YUKESH0620/ESP32-C3-Sensor-PCB/hardware_v0.2_Improved/Kicad_files_v0.2/images_v0.2/PCB_v0.2/Screenshot 2025-12-28 115842.png

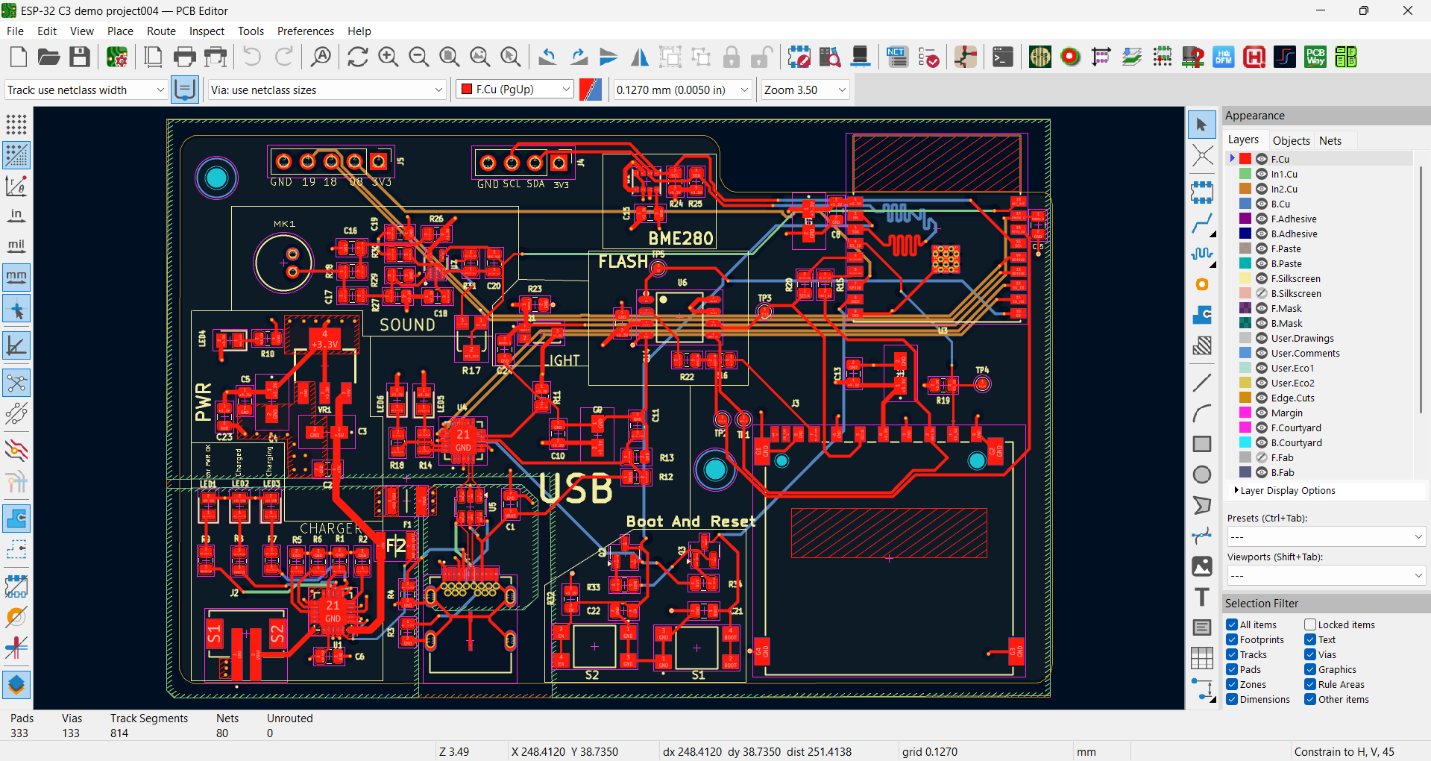
hardware_v0.2_Improved/Kicad_files_v0.2/images_v0.2/PCB_v0.2/Screenshot 2025-12-28 115842.png
