YUKESH0620/ESP32-C3-Sensor-PCB/hardware_v0.2_Improved/Kicad_files_v0.2/images_v0.2/Schematic_View_v0.2/Screenshot 2025-12-30 061500.png

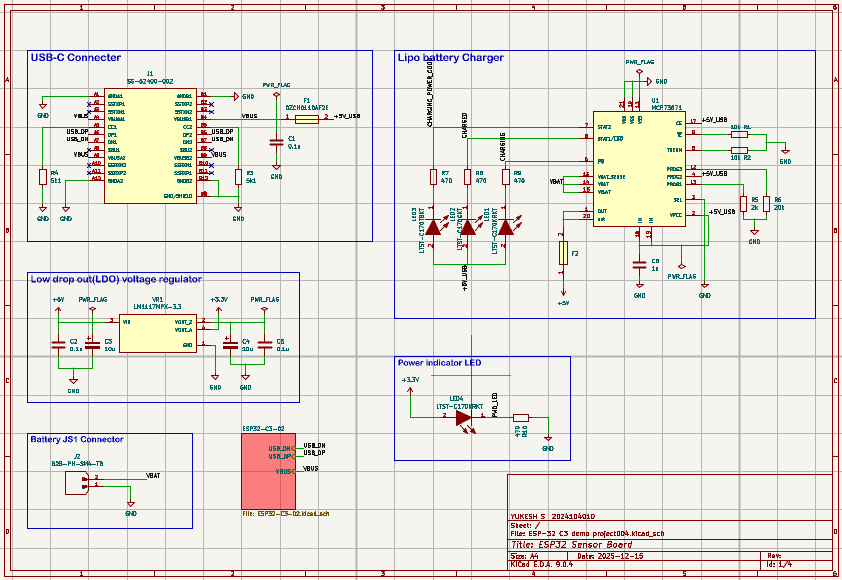
hardware_v0.2_Improved/Kicad_files_v0.2/images_v0.2/Schematic_View_v0.2/Screenshot 2025-12-30 061500.png
