YUKESH0620/ESP32-C3-Sensor-PCB/images/PCB_Layout/Screenshot 2025-12-26 091120.png

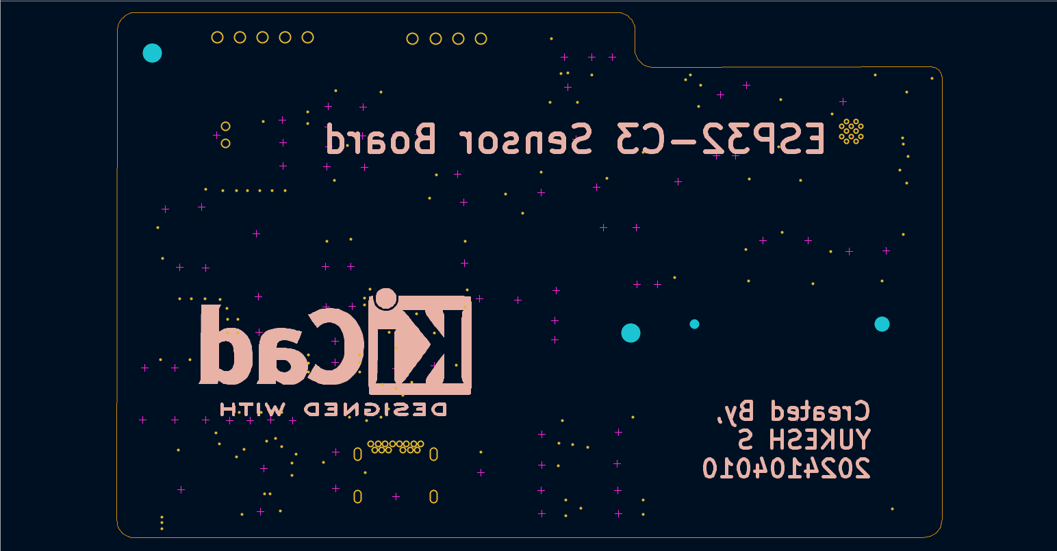
images/PCB_Layout/Screenshot 2025-12-26 091120.png
