YUKESH0620/ESP32-C3-Sensor-PCB/docs/External_Design_Blocks/USLPT2819DT2TR.step

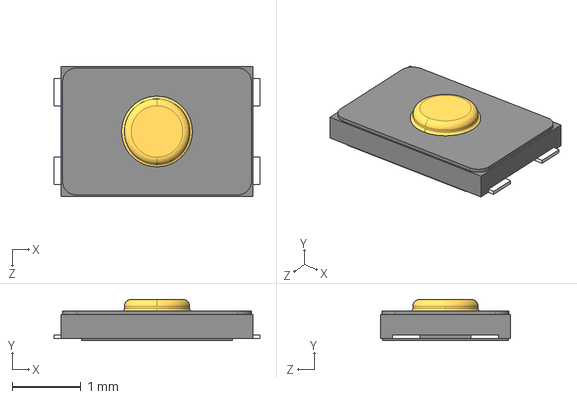
[picture p31: CAD file, 2025-12-26]
docs/External_Design_Blocks/USLPT2819DT2TR.step
3.00 x 0.6 x 1.90 mm
