YUKESH0620/ESP32-C3-Sensor-PCB/docs/External_Design_Blocks/TP4056.step

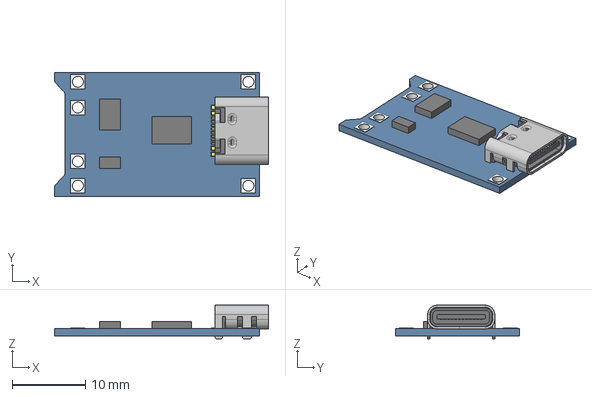
[picture p32: CAD file, 2025-12-26]
docs/External_Design_Blocks/TP4056.step
29.3 x 17.0 x 4.60 mm
