YUKESH0620/ESP32-C3-Sensor-PCB/docs/External_Design_Blocks/USB4110GFA.step

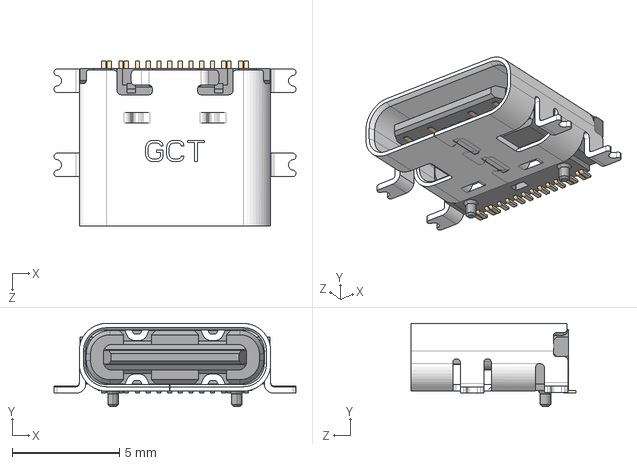
[picture p33: CAD file, 2025-12-26]
docs/External_Design_Blocks/USB4110GFA.step
11.3 x 3.89 x 7.70 mm
