YUKESH0620/ESP32-C3-Sensor-PCB/docs/External_Design_Blocks/1-2295018-2.step

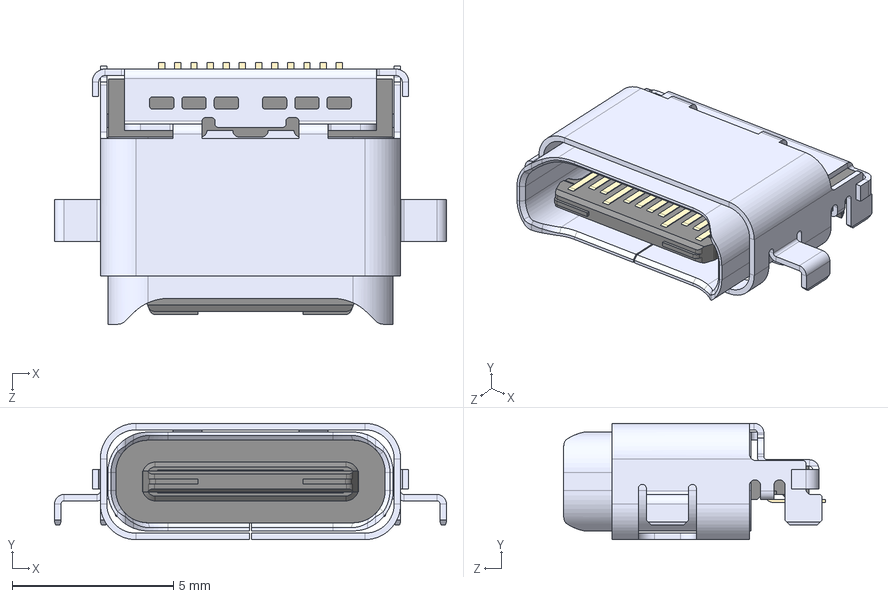
[picture p34: CAD file, 2025-12-26]
docs/External_Design_Blocks/1-2295018-2.step
12.1 x 3.60 x 8.10 mm
