YUKESH0620/ESP32-C3-Sensor-PCB/hardware/Schematic_view/ESP32-C3-02.kicad_sch

## KiCad design hardware/Schematic_view/ESP32-C3-02.kicad_sch (2025-12-26)

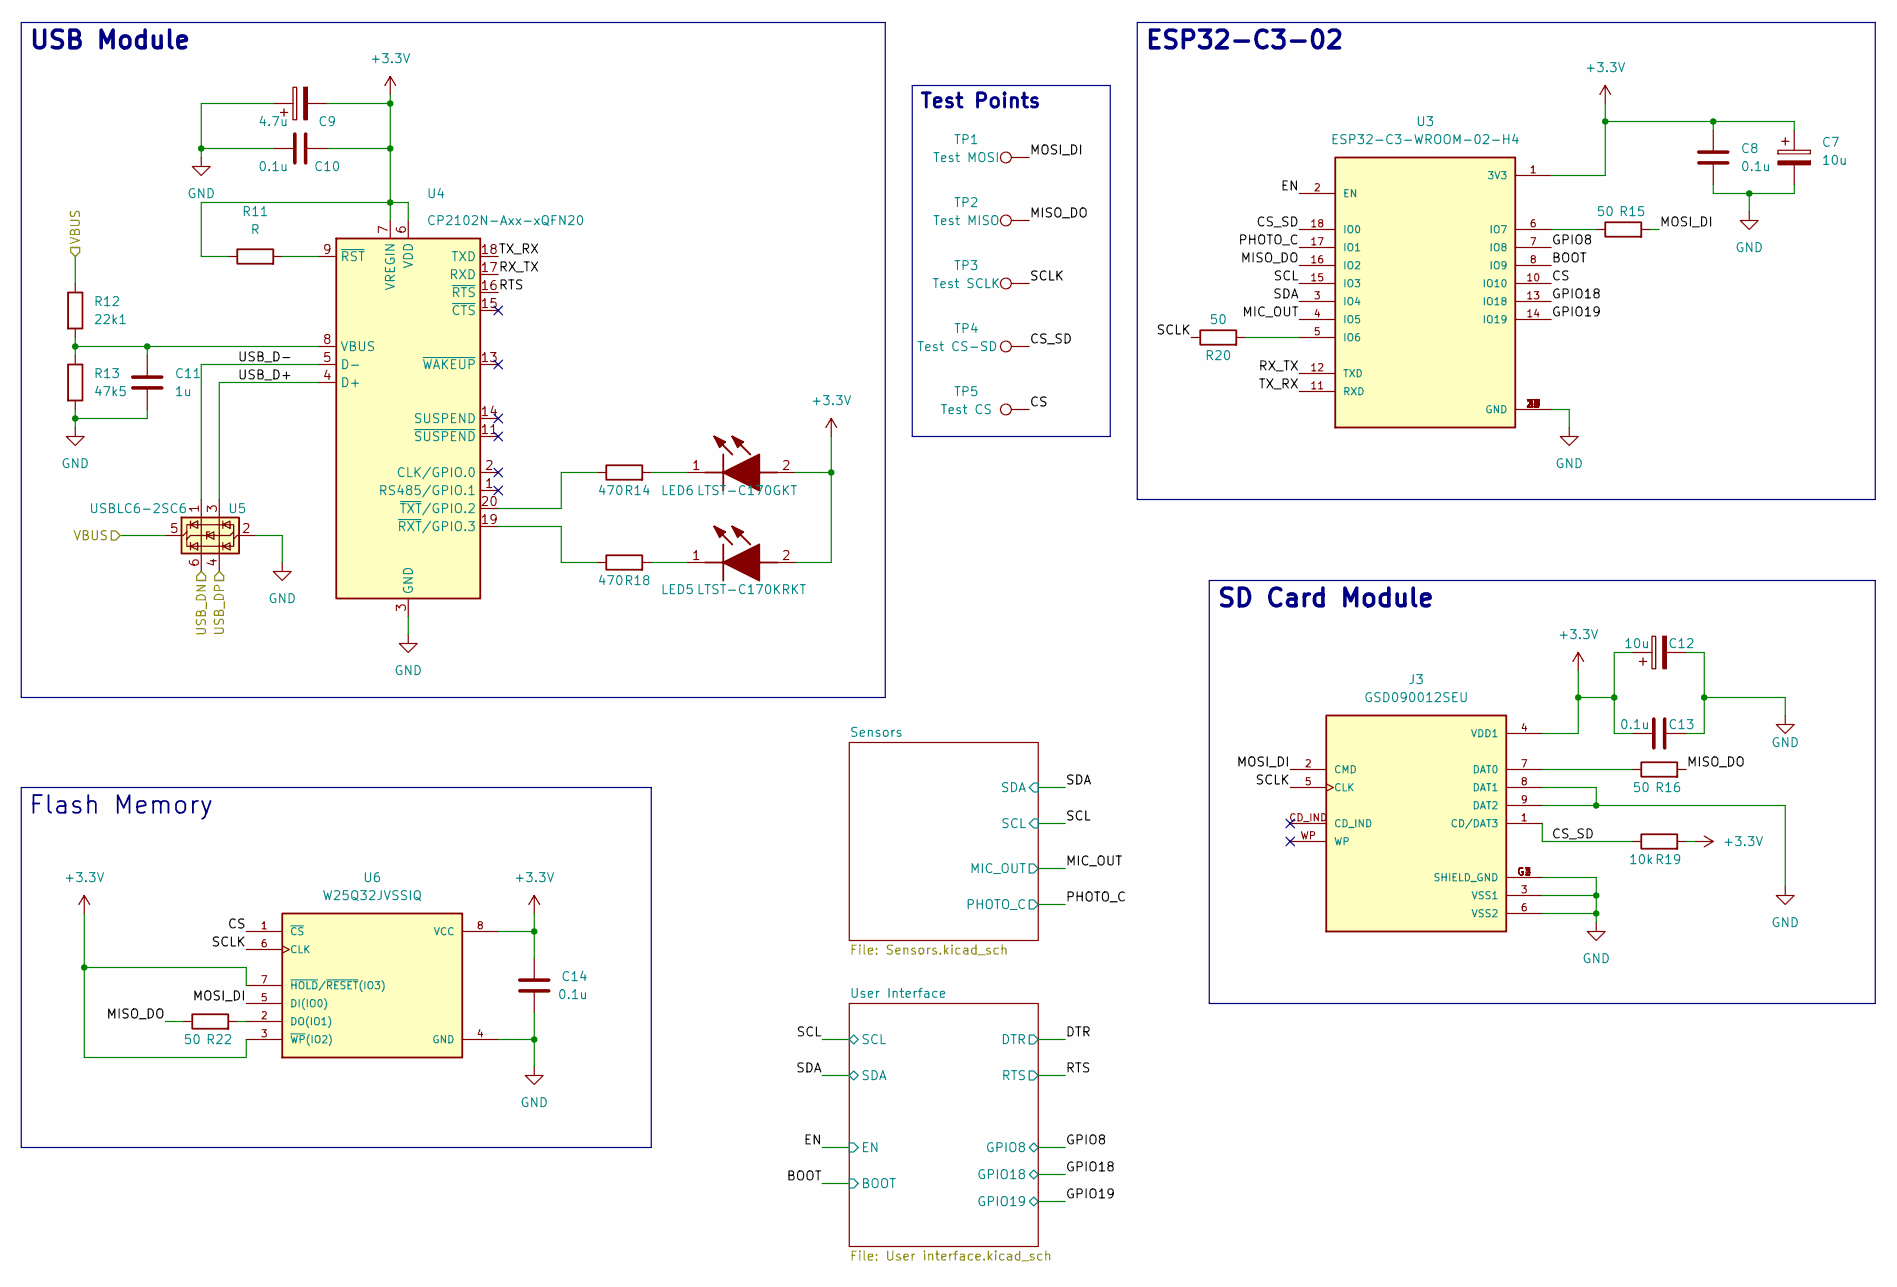
[picture p36: schematic ESP32-C3-02.kicad_sch]

Parts:
C7, C12: 10u; T491A
C8, C10, C13, C14: 0.1u; C_0805_2012Metric
C9: 4.7u; T491A
C11: 1u; C_0805_2012Metric
J3: GSD090012SEU; AMPHENOL_GSD090012SEU; PARTREV E
LED5: LTST-C170GKT; LEDC2012X120N; Manufacturer_Part_Number LTST-C170GKT; Mouser Part Number 859-LTST-C170GKT
LED6: LTST-C170KRKT; LEDC2012X120N; Manufacturer_Part_Number LTST-C170KRKT; Mouser Part Number 859-LTST-C170KRKT
R11: R; R_0805_2012Metric
R12: 22k1; R_0805_2012Metric
R13: 47k5; R_0805_2012Metric
R14, R18: 470; R_0805_2012Metric
R15, R16, R20, R22: 50; R_0805_2012Metric
R19: 10k; R_0805_2012Metric
TP1: Test MOSI; TestPoint_Pad_D1.0mm
TP2: Test MISO; TestPoint_Pad_D1.0mm
TP3: Test SCLK; TestPoint_Pad_D1.0mm
TP4: Test CS-SD; TestPoint_Pad_D1.0mm
TP5: Test CS; TestPoint_Pad_D1.0mm
U3: ESP32-C3-WROOM-02-H4; MODULE_ESP32-C3-WROOM-02-H4
U4: CP2102N-Axx-xQFN20; QFN50P400X400X100-21N
U5: USBLC6-2SC6; SOT-23-6
U6: W25Q32JVSSIQ; SOIC127P790X216-8N; M_PART_NUMBER W25QXX

Connections:
+3.3V: C7.1, C8.1, C9.2, C10.2, C12.1, C13.1, C14.2, J3.4 (VDD1), LED5.2 (A), LED6.2 (A), R11.1, R19.2, U3.1 (3V3), U4.6 (VDD), U4.7 (VREGIN), U6.3 (~WP(IO2)), U6.7 (~HOLD/~RESET(IO3)), U6.8 (VCC)
BOOT: U3.8 (IO9)
CS: TP5.1, U3.10 (IO10), U6.1 (~CS)
CS_SD: J3.1 (CD/DAT3), R19.1, TP4.1, U3.18 (IO0)
EN: U3.2 (EN)
GND: C7.2, C8.2, C9.1, C10.1, C11.2, C12.2, C13.2, C14.1, J3.3 (VSS1), J3.6 (VSS2), J3.8 (DAT1), J3.9 (DAT2), J3.G1 (SHIELD_GND), J3.G2 (SHIELD_GND), J3.G3 (SHIELD_GND), J3.G4 (SHIELD_GND), R13.2, U3.9 (GND), U3.19 (GND), U3.20 (GND), U3.21 (GND), U3.22 (GND), U3.23 (GND), U3.24 (GND), U3.25 (GND), U3.26 (GND), U3.27 (GND), U3.28 (GND), U3.29 (GND), U3.30 (GND), U3.31 (GND), U3.32 (GND), U3.33 (GND), U3.34 (GND), U3.35 (GND), U3.36 (GND), U3.37 (GND), U3.38 (GND), U3.39 (GND), U4.3 (GND), U4.12 (GND), U4.21 (GND), U5.2 (GND), U6.4 (GND)
GPIO8: U3.7 (IO8)
GPIO18: U3.13 (IO18)
GPIO19: U3.14 (IO19)
MIC_OUT: U3.4 (IO5)
MISO_DO: R16.2, R22.1, TP2.1, U3.16 (IO2)
MOSI_DI: J3.2 (CMD), R15.2, TP1.1, U6.5 (DI(IO0))
unnamed: C11.1, R12.2, R13.1, U4.8 (VBUS)
unnamed: J3.7 (DAT0), R16.1
unnamed: LED5.1 (K), R14.2
unnamed: LED6.1 (K), R18.2
unnamed: R11.2, U4.9 (~RST)
unnamed: R14.1, U4.20 (~TXT/GPIO.2)
unnamed: R15.1, U3.6 (IO7)
unnamed: R18.1, U4.19 (~RXT/GPIO.3)
unnamed: R20.2, U3.5 (IO6)
unnamed: R22.2, U6.2 (DO(IO1))
PHOTO_C: U3.17 (IO1)
RTS: U4.16 (~RTS)
RX_TX: U3.12 (TXD), U4.17 (RXD)
SCL: U3.15 (IO3)
SCLK: J3.5 (CLK), R20.1, TP3.1, U6.6 (CLK)
SDA: U3.3 (IO4)
TX_RX: U3.11 (RXD), U4.18 (TXD)
USB_D+: U4.4 (D+), U5.3 (I/O2)
USB_D-: U4.5 (D-), U5.1 (I/O1)
USB_DN: U5.6 (I/O1)
USB_DP: U5.4 (I/O2)
VBUS: R12.1, U5.5 (VBUS)

Notes on the sheet:
SD Card Module
Flash Memory
ESP32-C3-02
Test Points
USB Module
