YUKESH0620/ESP32-C3-Sensor-PCB/hardware/Schematic_view/ESP-32 C3 demo project004.kicad_sch

## KiCad design hardware/Schematic_view/ESP-32 C3 demo project004.kicad_sch (2025-12-26)

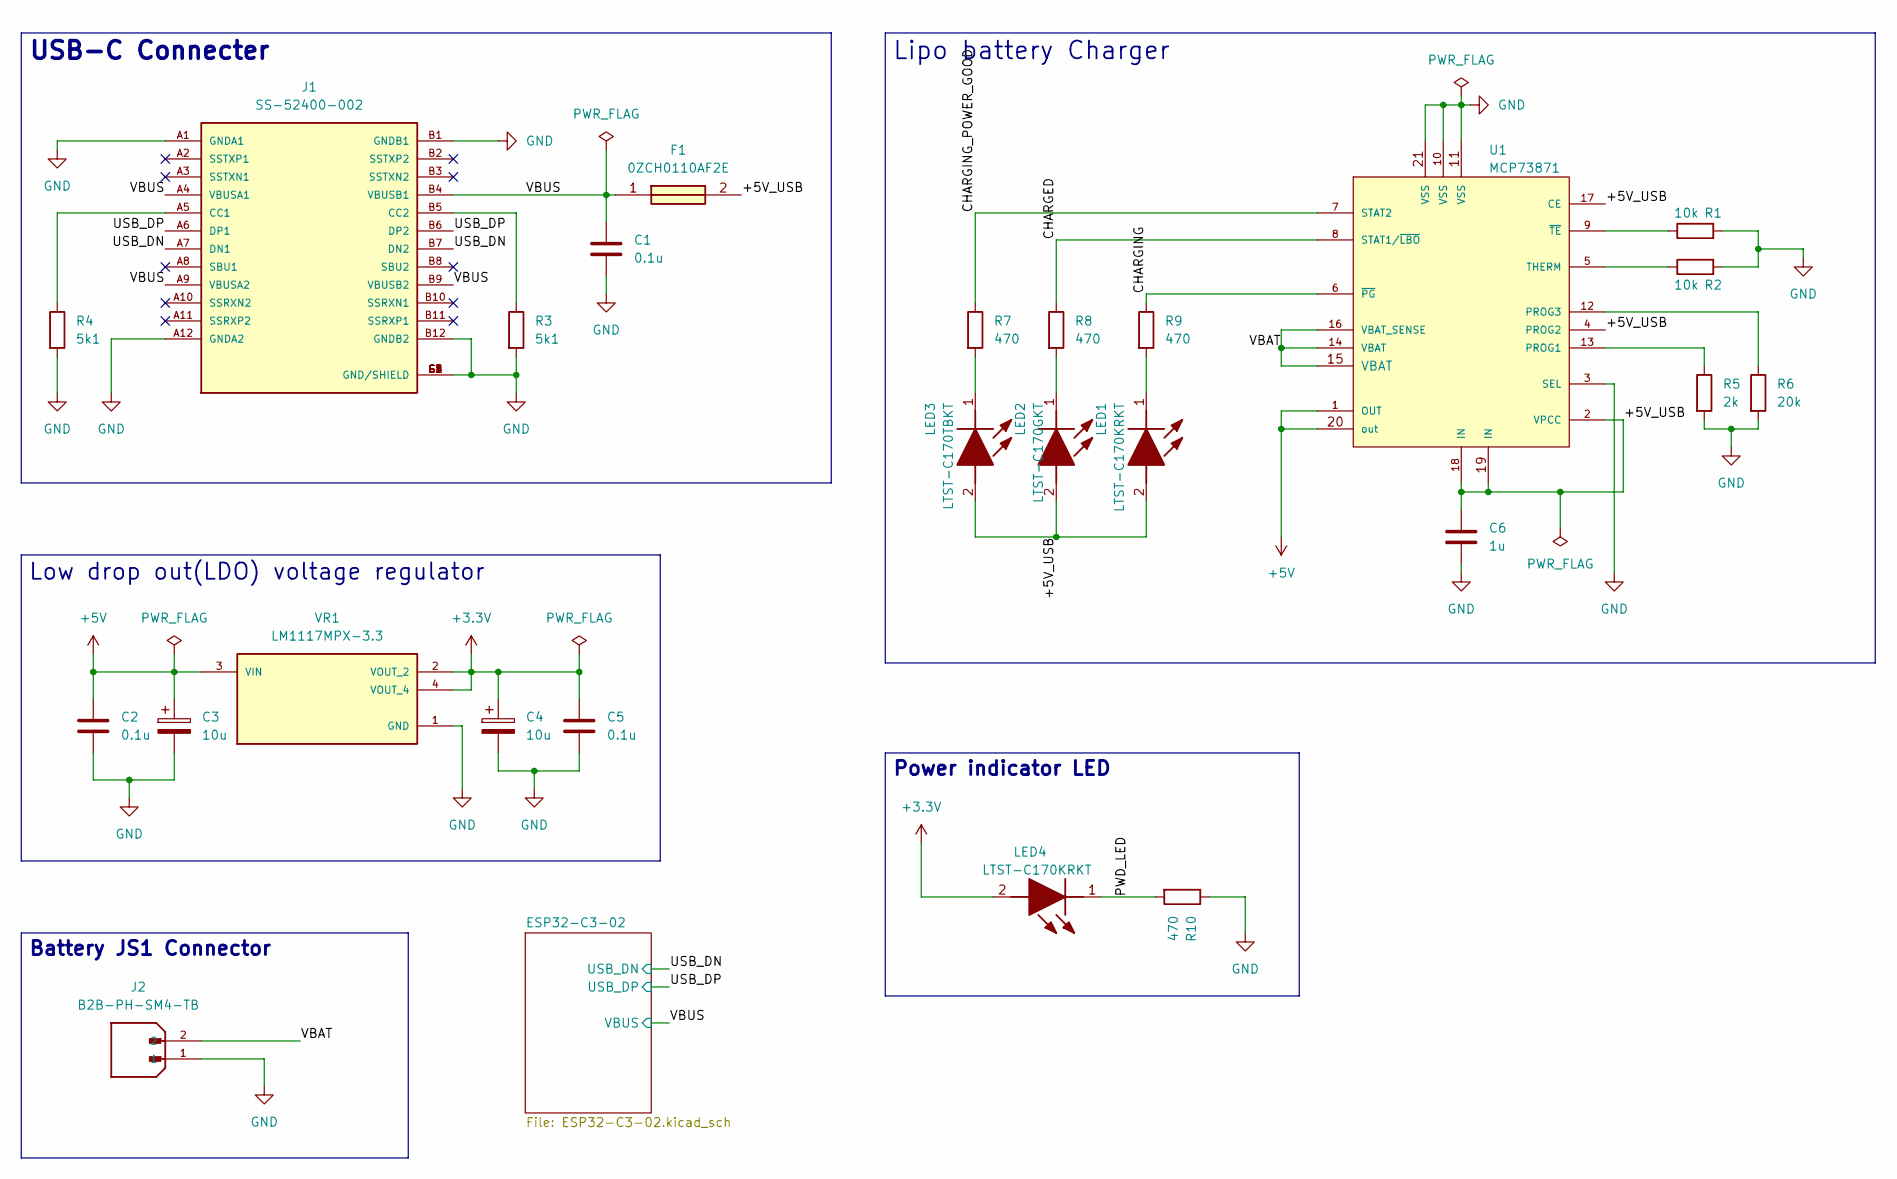
[picture p37: schematic ESP-32 C3 demo project004.kicad_sch]

Parts:
C1, C2, C5: 0.1u; C_0805_2012Metric
C3, C4: 10u; T491A
C6: 1u; C_0805_2012Metric
F1: 0ZCH0110AF2E; FUSC3226X100N; Manufacturer_Part_Number 0ZCH0110AF2E
J1: SS-52400-002; BELFUSE_SS-52400-002; PARTREV A0
J2: B2B-PH-SM4-TB; JST_B2B-PH-SM4-TB; PARTREV N/A
LED1, LED4: LTST-C170KRKT; LEDC2012X120N; Manufacturer_Part_Number LTST-C170KRKT; Mouser Part Number 859-LTST-C170KRKT
LED2: LTST-C170GKT; LEDC2012X120N; Manufacturer_Part_Number LTST-C170GKT; Mouser Part Number 859-LTST-C170GKT
LED3: LTST-C170TBKT; LEDC2012X120N; Manufacturer_Part_Number LTST-C170TBKT; Mouser Part Number 859-LTST-C170TBKT
R1, R2: 10k; R_0805_2012Metric
R3, R4: 5k1; R_0805_2012Metric
R5: 2k; R_0805_2012Metric
R6: 20k; R_0805_2012Metric
R7, R8, R9, R10: 470; R_0805_2012Metric
U1: MCP73871; QFN50P400X400X100-21N; PARTREV D
VR1: LM1117MPX-3.3; VREG_LM1117MPX-3.3

Connections:
+3.3V: C4.1, C5.1, LED4.2 (A), VR1.2 (VOUT_2), VR1.4 (VOUT_4)
+5V: C2.1, C3.1, U1.1 (OUT), U1.20 (out), VR1.3 (VIN)
+5V_USB: C6.1, F1.2, LED1.2 (A), LED2.2 (A), LED3.2 (A), U1.2 (VPCC), U1.4 (PROG2), U1.17 (CE), U1.18 (IN), U1.19 (IN)
CHARGED: R8.1, U1.8 (STAT1/~LBO)
CHARGING: R9.1, U1.6 (~PG)
CHARGING_POWER_GOOD: R7.1, U1.7 (STAT2)
GND: C1.2, C2.2, C3.2, C4.2, C5.2, C6.2, J1.A1 (GNDA1), J1.A12 (GNDA2), J1.B1 (GNDB1), J1.B12 (GNDB2), J1.G1 (GND/SHIELD), J1.G2 (GND/SHIELD), J1.G3 (GND/SHIELD), J1.G4 (GND/SHIELD), J1.S1 (GND/SHIELD), J1.S2 (GND/SHIELD), J1.S3 (GND/SHIELD), J1.S4 (GND/SHIELD), J2.1, R1.2, R2.2, R3.2, R4.2, R5.2, R6.2, R10.1, U1.3 (SEL), U1.10 (VSS), U1.11 (VSS), U1.21 (VSS), VR1.1 (GND)
unnamed: J1.A5 (CC1), R4.1
unnamed: J1.B5 (CC2), R3.1
unnamed: LED1.1 (K), R9.2
unnamed: LED2.1 (K), R8.2
unnamed: LED3.1 (K), R7.2
unnamed: R1.1, U1.9 (~TE)
unnamed: R2.1, U1.5 (THERM)
unnamed: R5.1, U1.13 (PROG1)
unnamed: R6.1, U1.12 (PROG3)
PWD_LED: LED4.1 (K), R10.2
USB_DN: J1.A7 (DN1), J1.B7 (DN2)
USB_DP: J1.A6 (DP1), J1.B6 (DP2)
VBAT: J2.2, U1.14 (VBAT), U1.15 (VBAT), U1.16 (VBAT_SENSE)
VBUS: C1.1, F1.1, J1.A4 (VBUSA1), J1.A9 (VBUSA2), J1.B4 (VBUSB1), J1.B9 (VBUSB2)

Notes on the sheet:
Lipo battery Charger
USB-C Connecter
Power indicator LED
Battery JS1 Connector
Low drop out(LDO) voltage regulator
