YUKESH0620/ESP32-C3-Sensor-PCB/hardware/Schematic_view/Sensors.kicad_sch

## KiCad design hardware/Schematic_view/Sensors.kicad_sch (2025-12-26)

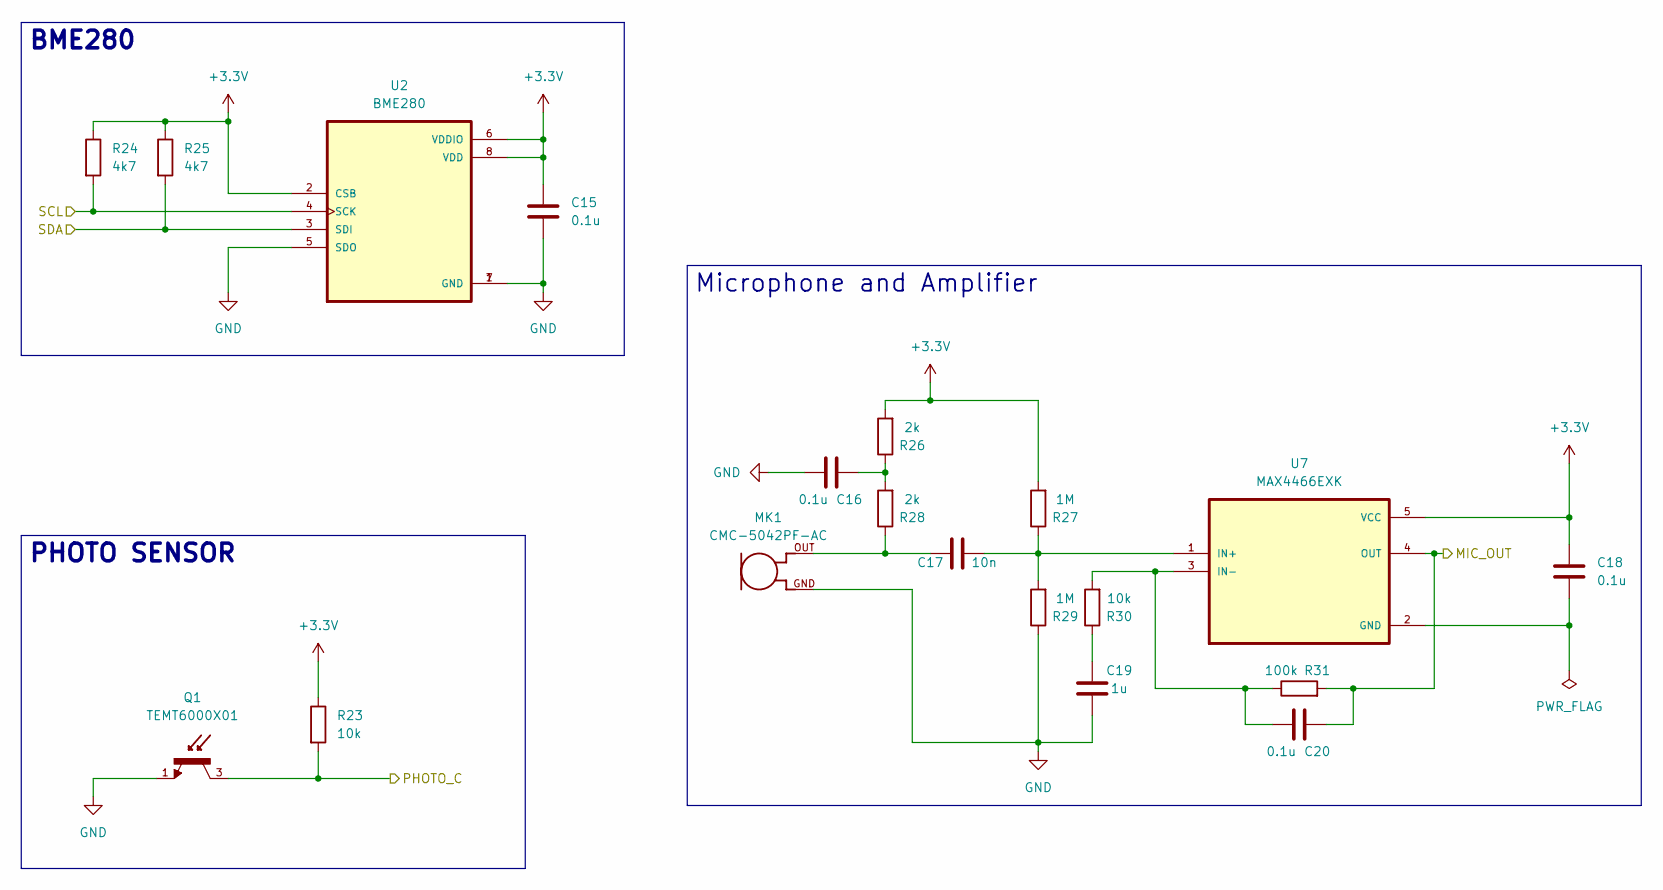
[picture p38: schematic Sensors.kicad_sch]

Parts:
C15, C16, C18, C20: 0.1u; C_0805_2012Metric
C17: 10n; C_0805_2012Metric
C19: 1u; C_0805_2012Metric
MK1: CMC-5042PF-AC; CUI_CMC-5042PF-AC
Q1: TEMT6000X01; TRANS_TEMT6000X01; PARTREV 1.9
R23, R30: 10k; R_0805_2012Metric
R24, R25: 4k7; R_0805_2012Metric
R26, R28: 2k; R_0805_2012Metric
R27, R29: 1M; R_0805_2012Metric
R31: 100k; R_0805_2012Metric
U2: BME280; PSON65P250X250X100-8N
U7: MAX4466EXK; SOT65P210X110-5N

Connections:
+3.3V: C15.1, C18.1, R23.1, R24.1, R25.1, R26.2, R27.2, U2.2 (CSB), U2.6 (VDDIO), U2.8 (VDD), U7.5 (VCC)
GND: C15.2, C16.1, C19.1, MK1.GND, Q1.1, R29.1, U2.1 (GND), U2.5 (SDO), U2.7 (GND)
MIC_OUT: C20.2, R31.2, U7.4 (OUT)
unnamed: C16.2, R26.1, R28.2
unnamed: C17.1, R27.1, R29.2, U7.1 (IN+)
unnamed: C17.2, MK1.OUT, R28.1
unnamed: C18.2, U7.2 (GND)
unnamed: C19.2, R30.1
unnamed: C20.1, R30.2, R31.1, U7.3 (IN-)
PHOTO_C: Q1.3, R23.2
SCL: R24.2, U2.4 (SCK)
SDA: R25.2, U2.3 (SDI)

Notes on the sheet:
BME280
Microphone and Amplifier
PHOTO SENSOR
