YUKESH0620/ESP32-C3-Sensor-PCB/hardware/Schematic_view/User interface.kicad_sch

## KiCad design hardware/Schematic_view/User interface.kicad_sch (2025-12-26)

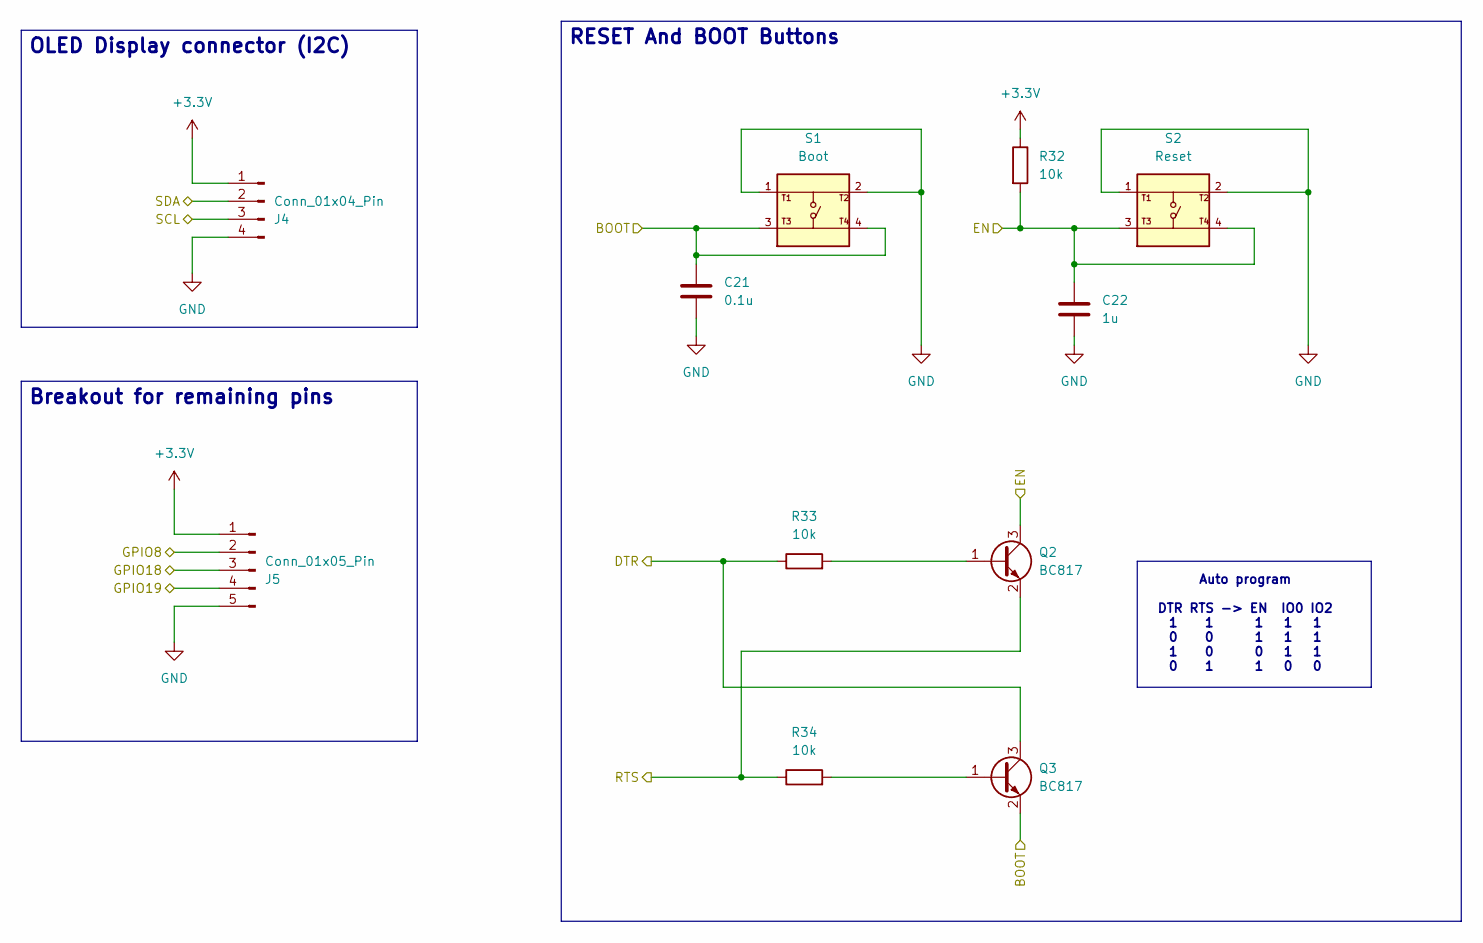
[picture p39: schematic User interface.kicad_sch]

Parts:
C21: 0.1u; C_0805_2012Metric
C22: 1u; C_0805_2012Metric
J4: Conn_01x04_Pin; PinHeader_1x04_P2.54mm_Vertical
J5: Conn_01x05_Pin; PinHeader_1x05_P2.54mm_Vertical
Q2, Q3: BC817; SOT-23
R32, R33, R34: 10k; R_0805_2012Metric
S1: Boot; SW_USLPT2819DT2TR; PARTREV P
S2: Reset; SW_USLPT2819DT2TR; PARTREV P

Connections:
+3.3V: J4.1, J5.1, R32.1
BOOT: C21.1, Q3.2 (E), S1.3, S1.4
DTR: Q3.3 (C), R33.1
EN: C22.1, Q2.3 (C), R32.2, S2.3, S2.4
GND: C21.2, C22.2, J4.4, J5.5, S1.1, S1.2, S2.1, S2.2
GPIO8: J5.2
GPIO18: J5.3
GPIO19: J5.4
unnamed: Q2.1 (B), R33.2
unnamed: Q3.1 (B), R34.2
RTS: Q2.2 (E), R34.1
SCL: J4.3
SDA: J4.2

Notes on the sheet:
Auto program DTR RTS -> EN IO0 IO2 1 1 1 1 1 0 0 1 1 1 1 0 0 1 1 0 1 1 0 0
Breakout for remaining pins
RESET And BOOT Buttons
OLED Display connector (I2C)
